VirgilVasiu/Arduino-PC-Interface/Design/AudioControllerSchematic_Photoresistor.sch

## EAGLE design Design/AudioControllerSchematic_Photoresistor.sch (2022-10-13)

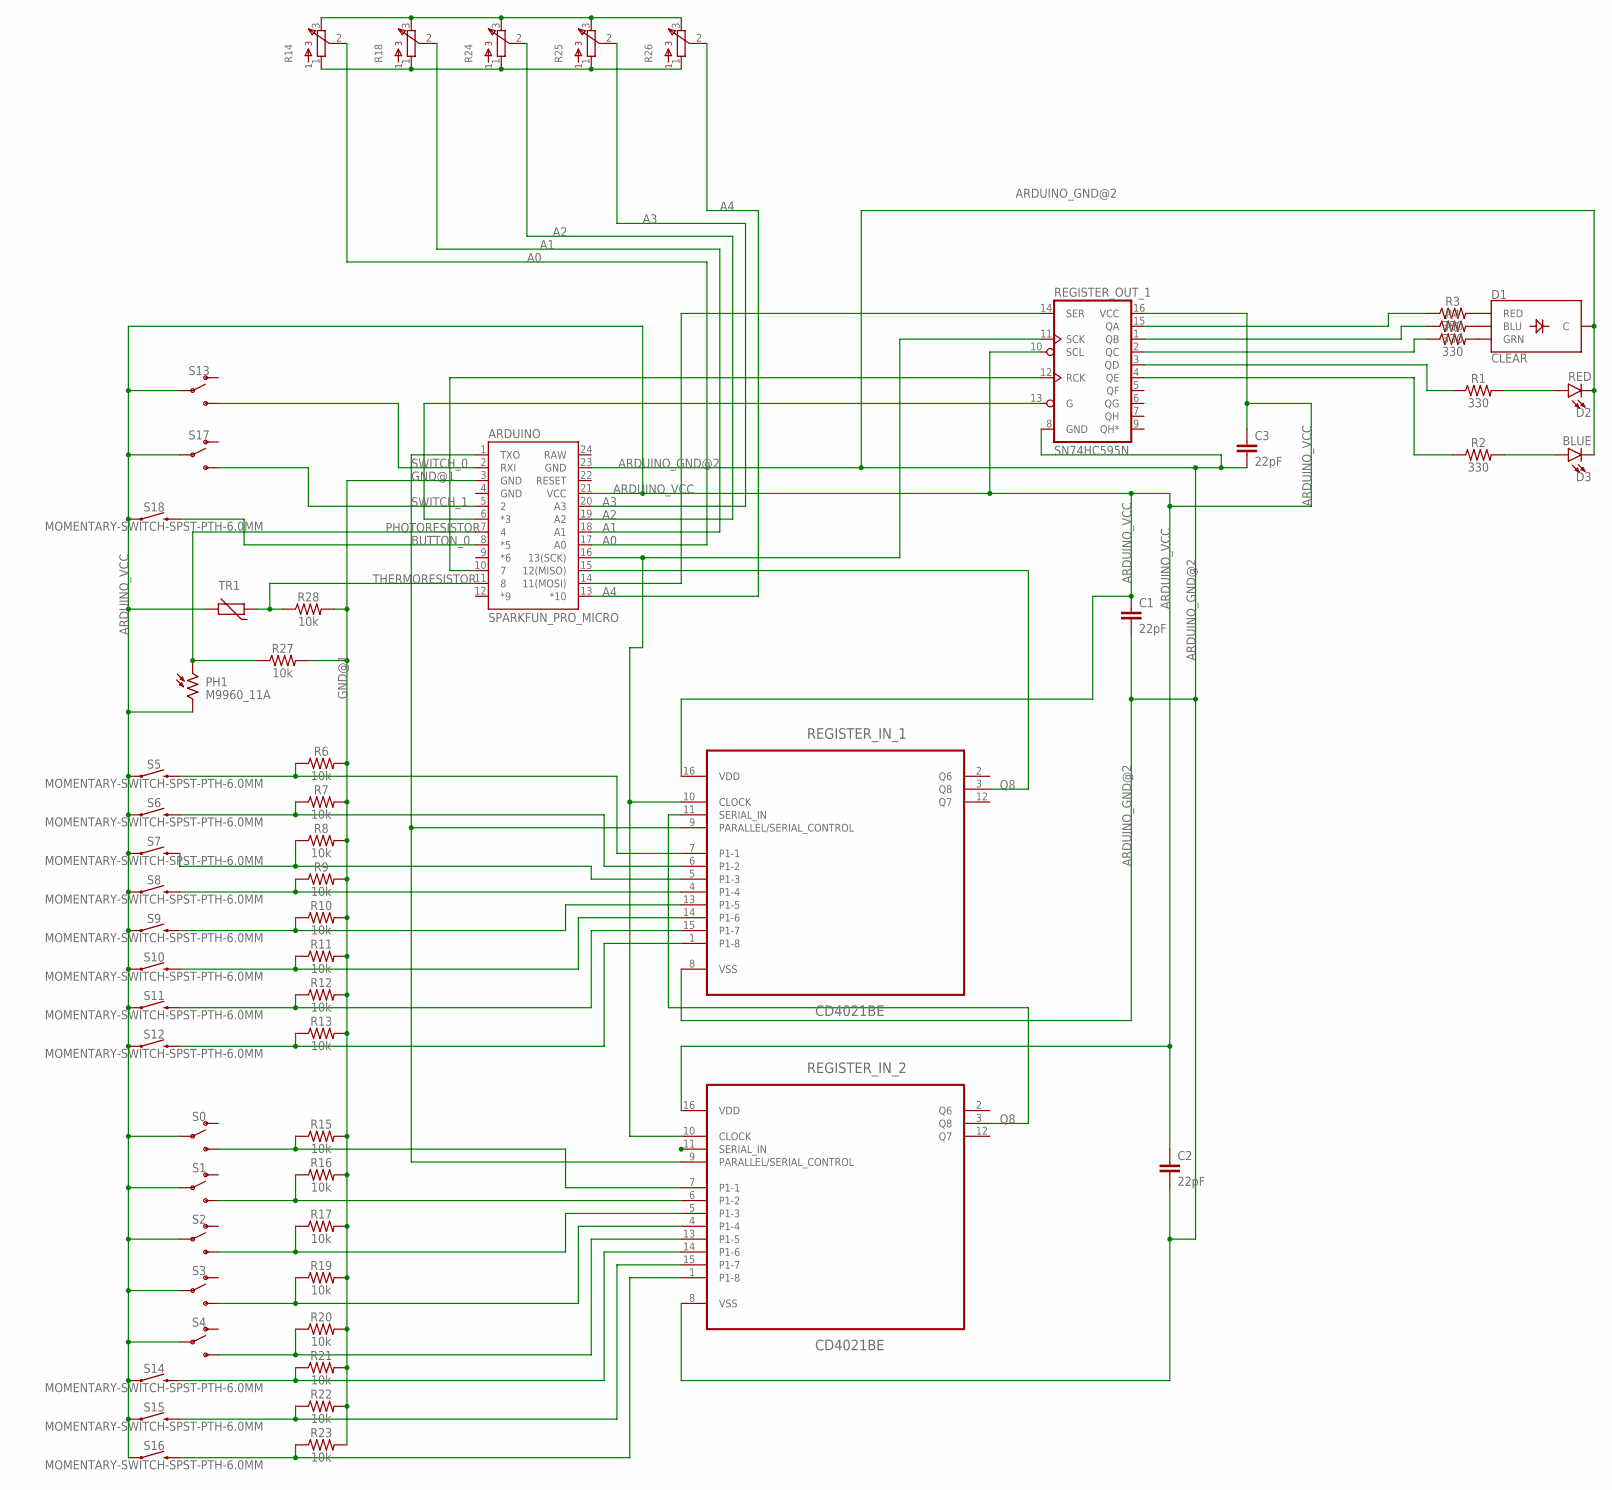
[picture p12: schematic AudioControllerSchematic_Photoresistor.sch]

Parts:
ARDUINO: SPARKFUN_PRO_MICRO
C1, C2, C3: 22pF; 0603
D1: CLEAR; LED-RGB-THRU
D2: RED; LED-0603
D3: BLUE; LED-0603
PH1: M9960_11A; M9960
R1, R2, R3, R4, R5: 330; 0603
R6, R7, R8, R9, R10, R11, R12, R13, R15, R16, R17, R19, R20, R21, R22, R23, R27, R28: 10k; 0603
R14, R18, R24, R25, R26: 91
REGISTER_IN_1, REGISTER_IN_2: CD4021BE; DIP254P762X508-16
REGISTER_OUT_1: SN74HC595N; DIP16
S0, S1, S2, S3, S4, S13, S17: SWITCH-SPDT-PTH-11.6X4.0MM; SWITCH_SPDT_PTH_11.6X4.0MM
S5, S6, S7, S8, S9, S10, S11, S12, S14, S15, S16, S18: MOMENTARY-SWITCH-SPST-PTH-6.0MM; TACTILE_SWITCH_PTH_6.0MM
TR1: THERMISTOR_R-2,5; RS-2,5

Connections:
A0: ARDUINO.17 (A0), R14.2
A1: ARDUINO.18 (A1), R18.2
A2: ARDUINO.19 (A2), R24.2
A3: ARDUINO.20 (A3), R25.2
A4: ARDUINO.13 (*10), R26.2
ARDUINO_GND@2: ARDUINO.23 (GND), C1.2, C2.2, C3.2, D1.2 (C), D2.C, D3.C, REGISTER_IN_1.8 (VSS), REGISTER_IN_2.8 (VSS), REGISTER_OUT_1.8 (GND)
ARDUINO_VCC: ARDUINO.21 (VCC), C1.1, C2.1, C3.1, PH1.2, REGISTER_IN_1.16 (VDD), REGISTER_IN_2.16 (VDD), REGISTER_OUT_1.10 (SCL), REGISTER_OUT_1.16 (VCC), S0.2, S1.2, S2.2, S3.2, S4.2, S5.1, S6.1, S7.1, S8.1, S9.1, S10.1, S11.1, S12.1, S13.2, S14.1, S15.1, S16.1, S17.2, S18.1, TR1.2
BUTTON_0: ARDUINO.8 (*5), S18.3 (2)
GND@1: ARDUINO.3 (GND), R6.2, R7.2, R8.2, R9.2, R10.2, R11.2, R12.2, R13.2, R15.2, R16.2, R17.2, R19.2, R20.2, R21.2, R22.2, R23.2, R27.2, R28.2
unnamed: R6.1, REGISTER_IN_1.7 (P1-1), S5.3 (2)
unnamed: R14.3, R18.3, R24.3, R25.3, R26.3
unnamed: ARDUINO.14 (11(MOSI)), REGISTER_OUT_1.14 (SER)
unnamed: ARDUINO.1 (TXO), REGISTER_IN_1.9 (PARALLEL/SERIAL_CONTROL), REGISTER_IN_2.9 (PARALLEL/SERIAL_CONTROL)
unnamed: ARDUINO.10 (7), REGISTER_OUT_1.12 (RCK)
unnamed: ARDUINO.6 (*3), REGISTER_OUT_1.13 (G)
unnamed: R7.1, REGISTER_IN_1.6 (P1-2), S6.3 (2)
unnamed: R8.1, REGISTER_IN_1.5 (P1-3), S7.3 (2)
unnamed: R9.1, REGISTER_IN_1.4 (P1-4), S8.3 (2)
unnamed: R10.1, REGISTER_IN_1.13 (P1-5), S9.3 (2)
unnamed: R11.1, REGISTER_IN_1.14 (P1-6), S10.3 (2)
unnamed: R12.1, REGISTER_IN_1.15 (P1-7), S11.3 (2)
unnamed: R13.1, REGISTER_IN_1.1 (P1-8), S12.3 (2)
unnamed: R15.1, REGISTER_IN_2.7 (P1-1), S0.3 (S)
unnamed: R16.1, REGISTER_IN_2.6 (P1-2), S1.3 (S)
unnamed: R19.1, REGISTER_IN_2.4 (P1-4), S3.3 (S)
unnamed: R20.1, REGISTER_IN_2.13 (P1-5), S4.3 (S)
unnamed: R21.1, REGISTER_IN_2.14 (P1-6), S14.3 (2)
unnamed: R22.1, REGISTER_IN_2.15 (P1-7), S15.3 (2)
unnamed: R23.1, REGISTER_IN_2.1 (P1-8), S16.3 (2)
unnamed: R17.1, REGISTER_IN_2.5 (P1-3), S2.3 (S)
unnamed: R5.1, REGISTER_OUT_1.2 (QC)
unnamed: R4.1, REGISTER_OUT_1.1 (QB)
unnamed: R3.1, REGISTER_OUT_1.15 (QA)
unnamed: R1.1, REGISTER_OUT_1.3 (QD)
unnamed: R2.1, REGISTER_OUT_1.4 (QE)
unnamed: D1.1 (RED), R3.2
unnamed: D1.4 (BLU), R4.2
unnamed: D1.3 (GRN), R5.2
unnamed: D2.A, R1.2
unnamed: D3.A, R2.2
unnamed: ARDUINO.16 (13(SCK)), REGISTER_IN_1.10 (CLOCK), REGISTER_IN_2.10 (CLOCK), REGISTER_OUT_1.11 (SCK)
unnamed: R14.1, R18.1, R24.1, R25.1, R26.1
PHOTORESISTOR: ARDUINO.7 (4), PH1.1, R27.1
Q8: ARDUINO.15 (12(MISO)), REGISTER_IN_1.3 (Q8), REGISTER_IN_1.11 (SERIAL_IN), REGISTER_IN_2.3 (Q8)
SWITCH_0: ARDUINO.2 (RXI), S13.3 (S)
SWITCH_1: ARDUINO.5 (2), S17.3 (S)
THERMORESISTOR: ARDUINO.11 (8), R28.1, TR1.1
